DRAMCO/LoRaWAN_EFM32/src/deep_sleep_app.c

/*  ____  ____      _    __  __  ____ ___
 * |  _ \|  _ \    / \  |  \/  |/ ___/ _ \
 * | | | | |_) |  / _ \ | |\/| | |  | | | |
 * | |_| |  _ <  / ___ \| |  | | |__| |_| |
 * |____/|_| \_\/_/   \_\_|  |_|\____\___/
 *                           research group
 *                             dramco.be/
 *
 *   KU Leuven - Technology Campus Gent,
 *   Gebroeders De Smetstraat 1,
 *   B-9000 Gent, Belgium
 *
 *         File: deep_sleep_app.c
 *      Created: 2017-09-21
 *       Author: Geoffrey Ottoy
 *
 *  Description: Example application.
 *  	Change line 136
 */

#if defined(APP_TYPE) && (APP_TYPE == DEEP_SLEEP_APP)

// Standard C libraries
#include <string.h>
#include <math.h>
#include <time.h>
#include <stdlib.h>

// "commissioning_mydev.h" contains keys & IDs associated to your LoRaWAN network application and device.
#include "Comissioning_mydev.h"
// "board.h" contains functionality to initialize and interface with the EFM32 and its peripherals
#include "board.h"
// "omux-board.h" contains functionality to interface with several lines (outputs) of the expansion board,
// through the use of the I2C output MUX on the expansion board.
#include "omux-board.h"
// "si7021-board.h" offers functionality to interface with the Happy Gecko on-board temperature and
// humidity sensor.
#include "si7021-board.h"
// "LoRaMac.h" provides access to the LoRaWAN MAC layer functions.
#include "LoRaMac.h"
// "em_emu.h" provides access to the EMLIB Energy Management Unit (EMU) which allows switching between Energy Modes.
#include "em_emu.h"
#include "em_chip.h"


#error Change the payload. Be creative! Comment this line out afterwards
static const uint8_t payload[] = "@GillesC says: Wonderful Tutorial!";
#define payloadLength sizeof(payload) -1 // -1 to exclude the null terminator \0 when dealing with strings in C

#define APP_SENSE_DUTYCYCLE					10000	// Milliseconds between two sensor readings
#define APP_DEFAULT_DATARATE				DR_5	// SF7 - BW125
#define APP_PORT_TEMP						1		// Application port for temperature readings
#define APP_PORT_RH							2		// Application port for relative humidity
#define APP_PORT_BTN						3		// Application port for button action
#define APP_PORT_MIXED						4		// Application port for mixed payloads
#define APP_TEMP_SIZE						2		// Number of bytes in a temperature reading
#define APP_RH_SIZE							2		// Number of bytes in a relative humidity reading
#define APP_BTN_SIZE						2		// Number of bytes in a relative humidity reading
#define APP_DATA_TEMP_MAX_SIZE				8		// Size of temperature data buffer
#define APP_DATA_RH_MAX_SIZE				8		// Size of humidity data buffer
#define APP_DATA_MIXED_MAX_SIZE				18		// Size of mixed data buffer
#define APP_ADR_ON                          1		// Whether we use Adaptive Data Rate or not
#define APP_CONFIRMED_MSG_ON                1		// Whether this example will transmit confirmed or unconfirmed packets

#if (OVER_THE_AIR_ACTIVATION == 0)
    static uint8_t  NwkSKey[] = LORAWAN_NWKSKEY;
    static uint8_t  AppSKey[] = LORAWAN_APPSKEY;
    static uint32_t DevAddr   = LORAWAN_DEVICE_ADDRESS;
#else
    static uint8_t DevEui[] = LORAWAN_DEVICE_EUI;
    static uint8_t AppEui[] = LORAWAN_APPLICATION_EUI;
    static uint8_t AppKey[] = LORAWAN_APPLICATION_KEY;
#endif


typedef enum DeviceState
{
    DEVICE_STATE_INIT,
    DEVICE_STATE_JOIN,
    DEVICE_STATE_SENSE,
	DEVICE_STATE_WAIT,
    DEVICE_STATE_SLEEP
} DeviceState_t;

DeviceState_t devState;

static uint32_t     TxDutyCycleTime;            // Defines the application data transmission duty cycle
static TimerEvent_t TxNextPacketTimer;          // Timer to handle the application data transmission duty cycle
static bool         NextTx = true;              // Indicates if a new packet can be sent

static bool SendFrame()
{
    McpsReq_t mcpsReq;
    LoRaMacTxInfo_t txInfo;

    if (LoRaMacQueryTxPossible(APP_BTN_SIZE, &txInfo) != LORAMAC_STATUS_OK)
    {
        // Send empty frame in order to flush MAC commands
        mcpsReq.Type = MCPS_UNCONFIRMED;
        mcpsReq.Req.Unconfirmed.fBuffer = NULL;
        mcpsReq.Req.Unconfirmed.fBufferSize = 0;
        mcpsReq.Req.Unconfirmed.Datarate = APP_DEFAULT_DATARATE;
    }
    else // Send the data
    {
        if (APP_CONFIRMED_MSG_ON)
        {
            // Send a confirmed packet
            mcpsReq.Type = MCPS_CONFIRMED;
            mcpsReq.Req.Confirmed.fPort = APP_PORT_BTN;
            mcpsReq.Req.Confirmed.fBuffer = payload;
            mcpsReq.Req.Confirmed.fBufferSize = payloadLength;
            mcpsReq.Req.Confirmed.NbTrials = 8;
            mcpsReq.Req.Confirmed.Datarate = APP_DEFAULT_DATARATE;
        }
        else
        {
            // Send an unconfirmed packet
            mcpsReq.Type = MCPS_UNCONFIRMED;
            mcpsReq.Req.Unconfirmed.fPort = APP_PORT_BTN;
            mcpsReq.Req.Unconfirmed.fBuffer = payload;
            mcpsReq.Req.Unconfirmed.fBufferSize = payloadLength;
            mcpsReq.Req.Unconfirmed.Datarate = APP_DEFAULT_DATARATE;
        }
    }

    if (LoRaMacMcpsRequest(&mcpsReq) == LORAMAC_STATUS_OK)
        return false;

    return true;
}

static void OnTxNextPacketTimerEvent(void)
{
    TimerStop(&TxNextPacketTimer);

    // Check if we have already joined a network
    MibRequestConfirm_t mibReq;
    mibReq.Type = MIB_NETWORK_JOINED;
    LoRaMacStatus_t status = LoRaMacMibGetRequestConfirm(&mibReq);
    if (status == LORAMAC_STATUS_OK)
    {
        // If we already joined then transmit data
        if (mibReq.Param.IsNetworkJoined == true)
        {
        	//devState = DEVICE_STATE_WAIT;
        	devState = DEVICE_STATE_SLEEP;
            NextTx = true;
        }
        else // We need to join before we can send data
        	devState = DEVICE_STATE_JOIN;
    }
}

static void McpsConfirm(McpsConfirm_t *mcpsConfirm)
{
    // Packet was send (and we have waited for replies)
    NextTx = true;
}

static void McpsIndication(McpsIndication_t *mcpsIndication)
{
    if (mcpsIndication->Status == LORAMAC_EVENT_INFO_STATUS_OK)
    {
        // Packet received
    }
}

static void MlmeConfirm(MlmeConfirm_t *mlmeConfirm)
{
    if (mlmeConfirm->Status == LORAMAC_EVENT_INFO_STATUS_OK)
    {
        // Check if the node has joined the network
        if (mlmeConfirm->MlmeRequest == MLME_JOIN)
        	devState = DEVICE_STATE_SENSE;
    }

    NextTx = true;
}

//static void MlmeIndication(MlmeIndication_t *mlmeIndication)
//{
//}

int main_deep_sleep( void )
{
    LoRaMacPrimitives_t LoRaMacPrimitives;
    LoRaMacCallback_t LoRaMacCallbacks;
    MibRequestConfirm_t mibReq;

    BoardInitMcu();
    BoardInitPeriph();

    srand(time(NULL));   // should only be called once

    devState = DEVICE_STATE_INIT;
    while (true)
    {
        switch (devState)
        {
            case DEVICE_STATE_INIT:
            {
                LoRaMacPrimitives.MacMcpsConfirm = McpsConfirm;
                LoRaMacPrimitives.MacMcpsIndication = McpsIndication;
                LoRaMacPrimitives.MacMlmeConfirm = MlmeConfirm;
                //LoRaMacPrimitives.MacMlmeIndication = MlmeIndication;
                //LoRaMacCallbacks.GetBatteryLevel = BoardGetBatteryLevel;
                //LoRaMacCallbacks.GetTemperatureLevel = NULL;
                LoRaMacInitialization(&LoRaMacPrimitives, &LoRaMacCallbacks);

                TimerInit(&TxNextPacketTimer, OnTxNextPacketTimerEvent);

                // Enable or disable Adaptive Data Rate
				mibReq.Type = MIB_ADR;
				mibReq.Param.AdrEnable = APP_ADR_ON;
				LoRaMacMibSetRequestConfirm(&mibReq);


                // Set whether this is a public or private network
                mibReq.Type = MIB_PUBLIC_NETWORK;
                mibReq.Param.EnablePublicNetwork = LORAWAN_PUBLIC_NETWORK;
               // mibReq.Param.UpLinkCounter
                LoRaMacMibSetRequestConfirm( &mibReq );

                // Add some channels other than the default 3 channels
                // Channel = { Frequency [Hz], { ( ( DrMax << 4 ) | DrMin ) }, Band }
                LoRaMacChannelAdd(3, (ChannelParams_t){867100000, {((DR_5 << 4) | DR_0)}, 0});
                LoRaMacChannelAdd(4, (ChannelParams_t){867300000, {((DR_5 << 4) | DR_0)}, 0});
                LoRaMacChannelAdd(5, (ChannelParams_t){867500000, {((DR_5 << 4) | DR_0)}, 0});

                // Set which channel to use for RX2
                mibReq.Type = MIB_RX2_CHANNEL;
                mibReq.Param.Rx2Channel = (Rx2ChannelParams_t){869525000, DR_3};
                LoRaMacMibSetRequestConfirm(&mibReq);

                devState = DEVICE_STATE_JOIN;
                break;
            }
            case DEVICE_STATE_JOIN:
            {
#if (OVER_THE_AIR_ACTIVATION != 0)
                MlmeReq_t mlmeReq;

                // Initialize LoRaMac device unique ID
                //BoardGetUniqueId(DevEui);

                mlmeReq.Type = MLME_JOIN;
                mlmeReq.Req.Join.DevEui = DevEui;
                mlmeReq.Req.Join.AppEui = AppEui;
                mlmeReq.Req.Join.AppKey = AppKey;

                if (NextTx == true)
                    LoRaMacMlmeRequest(&mlmeReq);

                devState = DEVICE_STATE_WAIT;
#else
                // Choose a random device address if not already defined in Comissioning.h
                if (DevAddr == 0)
                {
                    srand1(BoardGetRandomSeed());
                    DevAddr = randr(0, 0x01FFFFFF);
                }

                mibReq.Type = MIB_NET_ID;
                mibReq.Param.NetID = LORAWAN_NETWORK_ID;
                LoRaMacMibSetRequestConfirm(&mibReq);

                mibReq.Type = MIB_DEV_ADDR;
                mibReq.Param.DevAddr = DevAddr;
                LoRaMacMibSetRequestConfirm(&mibReq);

                mibReq.Type = MIB_NWK_SKEY;
                mibReq.Param.NwkSKey = NwkSKey;
                LoRaMacMibSetRequestConfirm(&mibReq);

                mibReq.Type = MIB_APP_SKEY;
                mibReq.Param.AppSKey = AppSKey;
                LoRaMacMibSetRequestConfirm(&mibReq);

                mibReq.Type = MIB_NETWORK_JOINED;
                mibReq.Param.IsNetworkJoined = true;
                LoRaMacMibSetRequestConfirm(&mibReq);

                devState = DEVICE_STATE_SENSE;
#endif
                break;
            }
            case DEVICE_STATE_SENSE:
            {
            	GpioWrite(&Led1, 1);
				SendFrame();
				GpioWrite(&Led1, 0);

				// Schedule next sensor reading
				TxDutyCycleTime = APP_SENSE_DUTYCYCLE;
				TimerSetValue(&TxNextPacketTimer, TxDutyCycleTime);
				TimerStart(&TxNextPacketTimer);

                devState = DEVICE_STATE_WAIT;
                break;
            }
            case DEVICE_STATE_WAIT:
            {
            	// Wake up through events
            	TimerLowPowerHandler();
            	break;
            }
            case DEVICE_STATE_SLEEP:
            {
                // Wake up through events
            	EMU_EnterEM3(true);
                break;
            }
        }
    }
}

// This function is called when PB0 is pressed
void Button_0_ISR(void){
	GpioToggle(&Led0);
}

// This function is called when PB1 is pressed
void Button_1_ISR(void){
	//OMuxToggleLed(&I2c);
	EMU_Restore();
	devState = DEVICE_STATE_SENSE;
}

#endif /* DEEP_SLEEP_APP */
