DRAMCO/LoRaWAN_EFM32/boards/rtc-board.h

/*
 / _____)             _              | |
( (____  _____ ____ _| |_ _____  ____| |__
 \____ \| ___ |    (_   _) ___ |/ ___)  _ \
 _____) ) ____| | | || |_| ____( (___| | | |
(______/|_____)_|_|_| \__)_____)\____)_| |_|
    (C)2013 Semtech

Description: MCU RTC timer and low power modes management

License: Revised BSD License, see LICENSE.TXT file include in the project

Maintainer: Miguel Luis and Gregory Cristian
*/
#ifndef __RTC_BOARD_H__
#define __RTC_BOARD_H__

/*!
 * \brief Temperature coefficient of the clock source
 */
//#define RTC_TEMP_COEFFICIENT                            ( -0.035 )

/*!
 * \brief Temperature coefficient deviation of the clock source
 */
//#define RTC_TEMP_DEV_COEFFICIENT                        ( 0.0035 )

/*!
 * \brief Turnover temperature of the clock source
 */
//#define RTC_TEMP_TURNOVER                               ( 25.0 )

/*!
 * \brief Turnover temperature deviation of the clock source
 */
//#define RTC_TEMP_DEV_TURNOVER                           ( 5.0 )

/*!
 * \brief Timer time variable definition
 */
typedef uint32_t TimerTime_t;

/*!
 * \brief Initializes the RTC timer
 *
 * \remark The timer is based on the RTC
 */
void RtcInit( void );

/*!
 * \brief Start the RTC timer
 *
 * \remark The timer is based on the RTC Alarm running at 32.768KHz
 *
 * \param[IN] timeout Duration of the Timer
 */
void RtcSetTimeout( uint32_t timeout );

/*!
 * \brief Adjust the value of the timeout to handle wakeup time from Alarm and GPIO irq
 *
 * \param[IN] timeout Duration of the Timer without compensation for wakeup time
 * \retval new value for the Timeout with compensations
 */
TimerTime_t RtcGetAdjustedTimeoutValue( uint32_t timeout );

/*!
 * \brief Get the RTC timer value
 *
 * \retval RTC Timer value
 */
TimerTime_t RtcGetTimerValue( void );

/*!
 * \brief Get the RTC timer elapsed time since the last Alarm was set
 *
 * \retval RTC Elapsed time since the last alarm
 */
TimerTime_t RtcGetElapsedAlarmTime( void );

/*!
 * \brief Compute the timeout time of a future event in time
 *
 * \param[IN] futureEventInTime Value in time
 * \retval time Time between now and the futureEventInTime
 */
TimerTime_t RtcComputeFutureEventTime( TimerTime_t futureEventInTime );

/*!
 * \brief Compute the elapsed time since a fix event in time
 *
 * \param[IN] eventInTime Value in time
 * \retval elapsed Time since the eventInTime
 */
TimerTime_t RtcComputeElapsedTime( TimerTime_t eventInTime );

/*!
 * \brief This function blocks the MCU from going into Low Power mode
 *
 * \param [IN] status [true: Enable, false: Disable
 */
void BlockLowPowerDuringTask ( bool status );

/*!
 * \brief Sets the MCU into low power STOP mode
 */
void RtcEnterLowPowerStopMode( void );

/*!
 * \brief Restore the MCU to its normal operation mode
 */
void RtcRecoverMcuStatus( void );

/*!
 * \brief Computes the temperature compensation for a period of time on a
 *        specific temperature.
 *
 * \param [IN] period Time period to compensate
 * \param [IN] temperature Current temperature
 *
 * \retval Compensated time period
 */
TimerTime_t RtcTempCompensation( TimerTime_t period, float temperature );


/*!
 * \brief Busy-wait for several milliseconds
 */
void HAL_Delay(uint32_t ms);


#endif // __RTC_BOARD_H__
